MRkuan/NODE_MCU_EXTEND/02_code/example/gaqu_spider/node_mcu_extend_pic.py

num_pic = ([
# 0
(0XFF,0XFF,0XFF,0XFF,0XFF,0XFF,0XE0,0X07,0XE0,0X07,0XE0,0X07,0XE0,0X07,0XE0,0X07,
0XE0,0X07,0XE0,0X07,0XE0,0X07,0XE0,0X07,0XE0,0X07,0XE0,0X07,0XE0,0X07,0XE0,0X07,
0XE0,0X07,0XE0,0X07,0XE0,0X07,0XE0,0X07,0XE0,0X07,0XE0,0X07,0XE0,0X07,0XE0,0X07,
0XE0,0X07,0XE0,0X07,0XE0,0X07,0XE0,0X07,0XE0,0X07,0XFF,0XFF,0XFF,0XFF,0XFF,0XFF),
#1
(0X07,0XC0,0X07,0XC0,0X07,0XC0,0X01,0XC0,0X01,0XC0,0X01,0XC0,0X01,0XC0,0X01,0XC0,
0X01,0XC0,0X01,0XC0,0X01,0XC0,0X01,0XC0,0X01,0XC0,0X01,0XC0,0X01,0XC0,0X01,0XC0,
0X01,0XC0,0X01,0XC0,0X01,0XC0,0X01,0XC0,0X01,0XC0,0X01,0XC0,0X01,0XC0,0X01,0XC0,
0X01,0XC0,0X01,0XC0,0X01,0XC0,0X01,0XC0,0X01,0XC0,0X01,0XC0,0X01,0XC0,0X01,0XC0),
#2
(0XFF,0XFF,0XFF,0XFF,0XFF,0XFF,0XE0,0X07,0X00,0X07,0X00,0X07,0X00,0X07,0X00,0X07,
0X00,0X07,0X00,0X07,0X00,0X07,0X00,0X07,0X00,0X07,0X00,0X07,0XFF,0XFF,0XFF,0XFF,
0XFF,0XFF,0XE0,0X00,0XE0,0X00,0XE0,0X00,0XE0,0X00,0XE0,0X00,0XE0,0X00,0XE0,0X00,
0XE0,0X00,0XE0,0X00,0XE0,0X00,0XE0,0X00,0XE0,0X07,0XFF,0XFF,0XFF,0XFF,0XFF,0XFF),
#3
(0XFF,0XFF,0XFF,0XFF,0XFF,0XFF,0XE0,0X07,0X00,0X07,0X00,0X07,0X00,0X07,0X00,0X07,
0X00,0X07,0X00,0X07,0X00,0X07,0X00,0X07,0X00,0X07,0X00,0X07,0X3F,0XFF,0X3F,0XFF,
0X3F,0XFF,0X00,0X07,0X00,0X07,0X00,0X07,0X00,0X07,0X00,0X07,0X00,0X07,0X00,0X07,
0X00,0X07,0X00,0X07,0X00,0X07,0X00,0X07,0XE0,0X07,0XFF,0XFF,0XFF,0XFF,0XFF,0XFF),
#4
(0XE0,0X07,0XE0,0X07,0XE0,0X07,0XE0,0X07,0XE0,0X07,0XE0,0X07,0XE0,0X07,0XE0,0X07,
0XE0,0X07,0XE0,0X07,0XE0,0X07,0XE0,0X07,0XE0,0X07,0XE0,0X07,0XFF,0XFF,0XFF,0XFF,
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
0X00,0X00,0X00,0X00,0X00,0X00,0X00,0X00,0X00,0X00,0X00,0X00,0X00,0X00,0X00,0X00,
0X00,0X00,0X00,0X00,0X00,0X00,0X00,0X00,0X00,0X00,0X00,0X00,0X00,0X00,0X00,0X00,
0X00,0X00,0X00,0X00,0X00,0X00,0X00,0X00,0X00,0X00,0X00,0X00,0X00,0X00,0X00,0X00)
